mkktop/OCFM_V2/App/app_flow_calc.c

/**
 * @file    app_flow_calc.c
 * @brief   流量计算模块实现
 * @details  实现明渠流量计的核心计算功能
 *          - 瞬时流量计算(巴歇尔槽、三角堰、矩形堰)
 *          - 累计流量计算
 *          - 单位换算
 *
 * @note    水位数据来源: app_sensor 模块
 *          配置数据来源: app_config 模块
 */

#include "app_flow_calc.h"
#include "app_config.h"
#include "rtc.h"
#include "at24c02.h"
#include "FreeRTOS.h"
#include "task.h"
#include <string.h>

/*============================================================================*/
/*                           私有类型                                          */
/*============================================================================*/

/**
 * @brief 巴歇尔水槽参数结构体
 * @details 基于CJ/T 3008.3-1993《巴歇尔量水槽》标准
 *          计算公式: Q = K * H^n
 *          其中: Q-流量(L/s), H-水位(m), K-流量系数, n-指数
 * @note   巴歇尔槽不使用Kh水头修正
 */
typedef struct {
    uint32_t number_ID;        /**< 水槽规格编号 (1-25: 1-17标准型, 18-25大型) */
    float width;               /**< 喉道宽度 (m) */
    float factor;              /**< 流量系数 K */
    float n;                   /**< 指数 n */
    float water_level_down;    /**< 最小水位限制 (m) */
    float water_level_up;      /**< 最大水位限制 (m) */
    float flow_range_down;     /**< 最小流量限制 (L/s) */
    float flow_range_up;       /**< 最大流量限制 (L/s) */
} Water_Channel;

/**
 * @brief 三角堰参数结构体
 * @details 基于ISO 1438标准 (Kindsvater-Shen方法)
 *          计算公式: Q = K * (H + Kh)^n
 *          其中: Q-流量(L/s), H-水位(m), K-流量系数, n=2.5, Kh-水头修正
 *          常用角度: 90°, 60°, 45°, 30°, 22.5°
 */
typedef struct {
    uint32_t number_ID;        /**< 堰型编号 (1-5) */
    float angle_deg;           /**< 堰口角度 (度) */
    float factor;              /**< 流量系数 K (含Ce) */
    float n;                   /**< 指数 n (固定2.5) */
    float kh;                  /**< 水头修正 Kh (m) */
    float water_level_down;    /**< 最小水位限制 (m) */
    float water_level_up;      /**< 最大水位限制 (m) */
    float flow_range_down;     /**< 最小流量限制 (L/s) */
    float flow_range_up;       /**< 最大流量限制 (L/s) */
} TriangularWeir_t;

/**
 * @brief 矩形堰参数结构体
 * @details 基于ISO 1438标准 (Francis公式 + Kh修正)
 *          计算公式: Q = K * b * (H + Kh)^1.5
 *          其中: Q-流量(L/s), H-水位(m), K-流量系数, b-堰宽(m), Kh-水头修正
 *          常用堰宽: 0.5m, 1.0m, 1.5m, 2.0m
 */
typedef struct {
    uint32_t number_ID;        /**< 堰型编号 (1-4) */
    float width;               /**< 堰宽 (m) */
    float factor;              /**< 流量系数 K (约1.838) */
    float n;                   /**< 指数 n (固定1.5) */
    float kh;                  /**< 水头修正 Kh (m) */
    float water_level_down;    /**< 最小水位限制 (m) */
    float water_level_up;      /**< 最大水位限制 (m) */
    float flow_range_down;     /**< 最小流量限制 (L/s) */
    float flow_range_up;       /**< 最大流量限制 (L/s) */
} RectangularWeir_t;

/**
 * @brief 累计流量EEPROM存储结构体
 */
typedef struct {
    uint32_t magic;            /**< 校验标志 */
    double total_flow;         /**< 累计流量 (m³) */
    uint32_t total_time;       /**< 累计时长 (秒) */
    uint32_t reserved;         /**< 保留字段 */
} TotalFlowStorage_t;

/*============================================================================*/
/*                           私有变量                                          */
/*============================================================================*/

static float s_instant_flow = 0.0f;     /**< 当前瞬时流量 (根据配置的单位) */
static float s_instant_flow_lps = 0.0f;  /**< 当前瞬时流量 (原始L/s，未经单位转换) */
static volatile float s_last_water_level_m = 0.0f; /**< 上次流量计算使用的水位 (米) */
static double s_total_flow_m3 = 0.0;    /**< 累计流量 (m³) */
static uint32_t s_total_time_sec = 0;   /**< 累计时长 (秒) */
static uint8_t s_bkp_save_counter = 0;  /**< 备份寄存器保存计数器 (10秒周期) */
static uint16_t s_eeprom_save_counter = 0; /**< EEPROM保存计数器 (5分钟周期) */
static volatile uint8_t s_eeprom_save_pending = 0; /**< EEPROM待保存标志 */

/*============================================================================*/
/*                           私有数据                                          */
/*============================================================================*/

/**
 * @brief 巴歇尔水槽参数表 (CJ/T 3008.3-1993)
 * @note  索引0-24对应规格1-25 (1-5小型, 6-17标准型, 18-25大型)
 *        公式: Q = K * H^n (L/s, m)
 *        1-17号标准型: K/n 取自 CJ/T 3008.3-1993 表3
 *        18-25号大型型: K 取自 CJ/T 3008.3-1993 表4 / ISO 9826 (n=1.6)
 */
static const Water_Channel s_channel_tbl[25] = {
    {  1, 0.025,   60.4, 1.550, 0.015, 0.21,   0.09,     5.4 },   /* 0.025m  */
    {  2, 0.051,  120.7, 1.550, 0.015, 0.24,   0.18,    13.2 },   /* 0.051m  */
    {  3, 0.076,  177.1, 1.550, 0.030, 0.33,   0.77,    32.1 },   /* 0.076m  */
    {  4, 0.152,  381.2, 1.540, 0.030, 0.45,   1.50,   111.0 },   /* 0.152m  */
    {  5, 0.228,  535.4, 1.530, 0.030, 0.60,   2.50,   251.0 },   /* 0.228m  */
    {  6, 0.250,  561.0, 1.513, 0.030, 0.60,   3.00,   250.0 },   /* 0.250m  */
    {  7, 0.300,  679.0, 1.521, 0.030, 0.75,   3.50,   400.0 },   /* 0.300m  */
    {  8, 0.450, 1038.0, 1.537, 0.030, 0.75,   4.50,   630.0 },   /* 0.450m  */
    {  9, 0.600, 1403.0, 1.548, 0.050, 0.75,  12.50,   850.0 },   /* 0.60m   */
    { 10, 0.750, 1772.0, 1.557, 0.060, 0.75,  25.00,  1100.0 },   /* 0.75m   */
    { 11, 0.900, 2147.0, 1.565, 0.060, 0.75,  30.00,  1250.0 },   /* 0.90m   */
    { 12, 1.000, 2397.0, 1.569, 0.060, 0.80,  30.00,  1500.0 },   /* 1.00m   */
    { 13, 1.200, 2904.0, 1.577, 0.060, 0.80,  35.00,  2000.0 },   /* 1.20m   */
    { 14, 1.500, 3668.0, 1.586, 0.060, 0.80,  45.00,  2500.0 },   /* 1.50m   */
    { 15, 1.800, 4440.0, 1.593, 0.080, 0.80,  80.00,  3000.0 },   /* 1.80m   */
    { 16, 2.100, 5222.0, 1.599, 0.080, 0.80,  95.00,  3600.0 },   /* 2.10m   */
    { 17, 2.400, 6004.0, 1.605, 0.080, 0.80,   100.00,  4000.0 },   /* 2.40m   标准型最大喉宽(K外推) */
    { 18, 3.050,  7463.0, 1.600, 0.090, 1.07,  160.00,  8280.0 },   /* 3.05m   大型(10ft) */
    { 19, 3.660,  8859.0, 1.600, 0.090, 1.37,  190.00, 14680.0 },   /* 3.66m   大型(12ft) */
    { 20, 4.570, 10960.0, 1.600, 0.090, 1.67,  230.00, 25040.0 },   /* 4.57m   大型(15ft) */
    { 21, 6.100, 14450.0, 1.600, 0.090, 1.83,  310.00, 37970.0 },   /* 6.10m   大型(20ft) */
    { 22, 7.620, 17940.0, 1.600, 0.090, 1.83,  380.00, 47160.0 },   /* 7.62m   大型(25ft,K公式推导) */
    { 23, 9.140, 21440.0, 1.600, 0.090, 1.83,  460.00, 56330.0 },   /* 9.14m   大型(30ft) */
    { 24, 12.19, 28430.0, 1.600, 0.090, 1.83,  600.00, 74700.0 },   /* 12.19m  大型(40ft,K公式推导) */
    { 25, 15.24, 35410.0, 1.600, 0.090, 1.83,  750.00, 93040.0 },   /* 15.24m  大型(50ft) */
};

/**
 * @brief 三角堰参数表 (ISO 1438, Kindsvater-Shen方法)
 * @note  索引0-4对应规格1-5
 *        规格: 90°三角堰, 60°三角堰, 45°三角堰, 30°三角堰, 22.5°三角堰
 *        公式: Q = K * (H + Kh)^2.5 (L/s, m)
 *        K = Ce × (8/15) × √(2g) × tan(θ/2) × 1000
 *        Ce, Kh 由 Kindsvater-Shen 曲线拟合得到
 *        Ce = 0.607165052 - 0.000874467θ + 6.103933e-6 θ²
 *        Kh(ft) = 0.01449 - 0.0003396θ + 3.298e-6 θ² - 1.062e-8 θ³
 *        Kh(m) = Kh(ft) × 0.3048; 90°时 Kh=0.00085m (ISO 1438-1 标准 0.85mm)
 */
static const TriangularWeir_t s_triangular_weir_tbl[5] = {
    { 1,  90.0f, 1365.0f, 2.50f, 0.00085f, 0.05f, 0.40f,  0.88f,  140.7f },  /* 90° Ce=0.5779 Kh=0.00085m (ISO1438 0.85mm) */
    { 2,  60.0f,  786.4f, 2.50f, 0.00113f, 0.05f, 0.35f,  0.48f,   57.7f },  /* 60° Ce=0.5767 Kh=0.00113m */
    { 3,  45.0f,  567.8f, 2.50f, 0.00150f, 0.05f, 0.30f,  0.35f,   28.4f },  /* 45° Ce=0.5802 Kh=0.00150m */
    { 4,  30.0f,  371.1f, 2.50f, 0.00213f, 0.05f, 0.25f,  0.23f,   11.9f },  /* 30° Ce=0.5864 Kh=0.00213m */
    { 5,  22.5f,  277.5f, 2.50f, 0.00256f, 0.05f, 0.25f,  0.18f,    8.90f }, /* 22.5° Ce=0.5906 Kh=0.00256m */
};

/**
 * @brief 矩形堰参数表 (ISO 1438, Francis公式)
 * @note  索引0-3对应规格1-4
 *        规格: 0.5m堰宽, 1.0m堰宽, 1.5m堰宽, 2.0m堰宽
 *        公式: Q = K * b * (H + Kh)^1.5 (L/s, m) - 无侧收缩（全宽堰）
 *        K = Cd × (2/3) × √(2g) × 1000, Cd=0.622 (Francis)
 *        Kh ≈ 0.001m (Kindsvater-Carter 水头修正)
 */
static const RectangularWeir_t s_rectangular_weir_tbl[4] = {
    { 1, 0.50f, 1838.0f, 1.50f, 0.001f, 0.05f, 0.50f,  10.6f,  326.0f },   /* 0.5m堰宽 */
    { 2, 1.00f, 1838.0f, 1.50f, 0.001f, 0.05f, 0.60f,  21.2f,  856.0f },   /* 1.0m堰宽 */
    { 3, 1.50f, 1838.0f, 1.50f, 0.001f, 0.05f, 0.70f,  31.8f, 1618.0f },   /* 1.5m堰宽 */
    { 4, 2.00f, 1838.0f, 1.50f, 0.001f, 0.05f, 0.80f,  42.3f, 2635.0f },   /* 2.0m堰宽 */
};

/**
 * @brief  计算巴歇尔槽瞬时流量
 * @param  water_level_m: 水位 (米)
 * @param  channel: 水槽参数指针
 * @param  wl_down: 用户配置的水位下限 (m)
 * @param  wl_up: 用户配置的水位上限 (m)
 * @retval 瞬时流量 (L/s)，水位无效时返回0
 * @note   公式: Q = K * H^n，超量程时限制在最大值
 */
static float parshall_flow_Ls(float water_level_m, const Water_Channel *channel,
                              float wl_down, float wl_up)
{
    float Q = 0.0f;

    /* 检查空指针 */
    if (channel == NULL) {
        return 0.0f;
    }

    /* 水位高于上限: 钳位到上限计算 */
    if (water_level_m > wl_up) {
        Q = channel->factor * powf(wl_up, channel->n);
    }
    /* 水位低于下限 (扣除 0.1mm 容差，防止浮点精度边界误判)
     * 例: 高度800mm - 距离720mm 经 float 运算后为 0.07999998m，
     * 略小于下限 0.08f，数学上应相等却被判为"低于下限"，故加容差 */
    else if (water_level_m < wl_down - 0.0001f) {
        Q = 0.0f;
    }
    /* 水位在有效范围内 (含浮点容差区间 [wl_down-tol, wl_up]) */
    else {
        Q = channel->factor * powf(water_level_m, channel->n);
    }

    return Q;
}

/**
 * @brief  瞬时流量单位转换
 * @param  flow_l_s: 瞬时流量 (L/s)
 * @param  unit: 目标单位
 * @retval 转换后的瞬时流量值
 */
static float flow_convert_instant(float flow_l_s, flow_unit_t unit)
{
    switch (unit) {
        case FLOW_UNIT_L_S:
            return flow_l_s;
        case FLOW_UNIT_L_MIN:
            return flow_l_s * 60.0f;
        case FLOW_UNIT_L_H:
            return flow_l_s * 3600.0f;
        case FLOW_UNIT_M3_H:
            return flow_l_s * 3.6f;
        case FLOW_UNIT_M3_S:
            return flow_l_s / 1000.0f;
        case FLOW_UNIT_M3_MIN:
            return flow_l_s / 1000.0f * 60.0f;
        case FLOW_UNIT_T_H:
            return flow_l_s * 3.6f;
        case FLOW_UNIT_G_H:
            return flow_l_s * 3600.0f / 3.785411784f;
        default:
            return flow_l_s;
    }
}

/**
 * @brief  计算三角堰瞬时流量 (Kindsvater-Shen方法)
 * @param  water_level_m: 水位 (米)
 * @param  weir: 三角堰参数指针
 * @param  wl_down: 用户配置的水位下限 (m)
 * @param  wl_up: 用户配置的水位上限 (m)
 * @retval 瞬时流量 (L/s)，水位无效时返回0
 * @note   公式: Q = K * (H + Kh)^n，超量程时限制在最大值
 */
static float triangular_weir_flow_Ls(float water_level_m, const TriangularWeir_t *weir,
                                     float wl_down, float wl_up)
{
    float Q = 0.0f;
    float he;

    if (weir == NULL) {
        return 0.0f;
    }

    /* 水位高于上限: 钳位到上限计算 */
    if (water_level_m > wl_up) {
        he = wl_up + weir->kh;
        Q = weir->factor * powf(he, weir->n);
    }
    /* 水位低于下限 (扣除 0.1mm 容差，防止浮点精度边界误判) */
    else if (water_level_m < wl_down - 0.0001f) {
        Q = 0.0f;
    }
    /* 水位在有效范围内 (含浮点容差区间) */
    else {
        he = water_level_m + weir->kh;
        Q = weir->factor * powf(he, weir->n);
    }

    return Q;
}

/**
 * @brief  矩形堰 Kindsvater-Carter 收缩流量系数 Ce (ISO 1438-1 Figure 5)
 * @param  bB: 堰宽/渠宽比 b/B (0.2~1.0)
 * @param  hP: 水头/堰高比 h/P
 * @retval 流量系数 Ce (无量纲)
 * @note   按 b/B 分段(0.2~1.0 共9档) + h/P 线性插值查表
 *         表值取自 ISO 1438-1:2008 Figure 5 (Kindsvater-Carter 方法)
 *         不确定度: h/P<1.0 时 <=1.5%
 */
static float rect_weir_Ce(float bB, float hP)
{
    /* b/B = 1.0, 0.9, 0.8, ..., 0.2 共9档, 每档 h/P = 0.1,0.2,...,1.0 共8点 */
    static const float ce_tbl[9][8] = {
        /* h/P:  0.1    0.2    0.3    0.4    0.5    0.6    0.8    1.0  */
        /*1.0*/{0.610f,0.619f,0.627f,0.636f,0.644f,0.652f,0.669f,0.685f},
        /*0.9*/{0.609f,0.617f,0.626f,0.634f,0.642f,0.651f,0.668f,0.684f},
        /*0.8*/{0.608f,0.616f,0.624f,0.633f,0.641f,0.649f,0.666f,0.682f},
        /*0.7*/{0.606f,0.614f,0.623f,0.631f,0.639f,0.648f,0.664f,0.680f},
        /*0.6*/{0.603f,0.612f,0.620f,0.629f,0.637f,0.646f,0.662f,0.678f},
        /*0.5*/{0.600f,0.609f,0.617f,0.626f,0.634f,0.643f,0.659f,0.675f},
        /*0.4*/{0.596f,0.605f,0.613f,0.622f,0.630f,0.639f,0.655f,0.671f},
        /*0.3*/{0.590f,0.599f,0.608f,0.616f,0.625f,0.633f,0.650f,0.666f},
        /*0.2*/{0.583f,0.592f,0.601f,0.609f,0.618f,0.626f,0.643f,0.659f},
    };
    static const float hP_axis[8] = {0.1f,0.2f,0.3f,0.4f,0.5f,0.6f,0.8f,1.0f};
    int i_bB, i_hP;
    float w;

    if (bB > 1.0f) bB = 1.0f;            /* b/B 上限 1.0 (全宽堰) */
    if (bB < 0.2f) bB = 0.2f;            /* b/B 下限 0.2 (强收缩) */
    if (hP < 0.0f) hP = 0.0f;
    if (hP > 1.0f) hP = 1.0f;            /* KC 表适用 h/P<=1.0, 超出按1.0 */

    /* b/B 插值索引: 1.0->0, 0.9->1, ..., 0.2->8 (步长0.1) */
    {
        float fidx = (1.0f - bB) * 10.0f;
        i_bB = (int)fidx;
        if (i_bB > 7) i_bB = 7;          /* 保证 i_bB+1 不越界 */
        w = fidx - i_bB;
    }
    /* h/P 插值索引: 0.1->0, 0.2->1, ..., 0.8->6, 1.0->7 (非均匀: 0.6->0.8 跨0.2) */
    /* 简化: h/P<=0.6 用步长0.1, 0.6~0.8 跨0.2, 0.8~1.0 跨0.2 */
    {
        i_hP = 0;
        while (i_hP < 7 && hP > hP_axis[i_hP + 1]) i_hP++;
    }

    /* 双线性插值 (b/B, h/P) */
    {
        float Ce00 = ce_tbl[i_bB][i_hP];
        float Ce10 = ce_tbl[i_bB + 1][i_hP];
        float Ce01 = ce_tbl[i_bB][i_hP + 1];
        float Ce11 = ce_tbl[i_bB + 1][i_hP + 1];
        float hP_lo = hP_axis[i_hP];
        float hP_hi = hP_axis[i_hP + 1];
        float wh = (hP - hP_lo) / (hP_hi - hP_lo);
        if (wh < 0.0f) wh = 0.0f;
        if (wh > 1.0f) wh = 1.0f;
        float Ce_b_lo = Ce00 + w * (Ce10 - Ce00);
        float Ce_b_hi = Ce01 + w * (Ce11 - Ce01);
        return Ce_b_lo + wh * (Ce_b_hi - Ce_b_lo);
    }
}

/**
 * @brief  矩形堰 Kindsvater-Carter 宽度修正 Kb (ISO 1438-1 Figure 6)
 * @param  bB: 堰宽/渠宽比 b/B (0.2~1.0)
 * @retval 宽度修正 Kb (m), 全宽堰(b/B=1)返回0
 */
static float rect_weir_Kb(float bB)
{
    static const float kb_tbl[9] = {
        /* b/B: 1.0  0.9   0.8   0.7   0.6   0.5   0.4   0.3   0.2  */
              0.0f,0.0018f,0.0022f,0.0024f,0.0026f,0.0028f,0.0030f,0.0032f,0.0034f
    };
    int idx;
    if (bB > 1.0f) bB = 1.0f;
    if (bB < 0.2f) bB = 0.2f;
    idx = (int)((1.0f - bB) * 10.0f + 0.5f);   /* 四舍五入到最近档 */
    if (idx > 8) idx = 8;
    return kb_tbl[idx];
}

/**
 * @brief  计算矩形堰瞬时流量 (Kindsvater-Carter 方法, ISO 1438-1)
 * @param  water_level_m: 水位 (米)
 * @param  weir: 矩形堰参数指针
 * @param  wl_down: 用户配置的水位下限 (m)
 * @param  wl_up: 用户配置的水位上限 (m)
 * @retval 瞬时流量 (L/s)，水位无效时返回0
 * @note   公式: Q = Ce * (2/3) * sqrt(2g) * be * he^1.5
 *         he = H + Kh (Kh=0.001m 有效水头)
 *         全宽堰(B=0或B<=b): be=b, Ce=0.602+0.083*(H/P)
 *         收缩堰(B>b):       be=b+Kb, Ce 按 b/B,h/P 查 ISO Figure 5
 *         需堰高 P(weir_height) 配置; P=0 或 h/P>1.0 时回退到 Francis 固定系数
 *         (ISO KC 法适用范围: h/P<=1.0, P>=0.1m, h>=0.03m)
 *         超量程时钳位到上限计算
 */
static float rectangular_weir_flow_Ls(float water_level_m, const RectangularWeir_t *weir,
                                      float wl_down, float wl_up)
{
    float Q = 0.0f;
    float he, effective_width;
    float use_kc;   /* 1=Kindsvater-Carter, 0=Francis回退 */

    if (weir == NULL) {
        return 0.0f;
    }

    float B = app_config_get_channel_width() / 1000.0f;
    float b = weir->width;
    float P = app_config_get_weir_height() / 1000.0f;   /* 堰高(m), 0=未配置 */
    int   contracted = (B > 0.0f && b < B);             /* 是否收缩堰 */

    /* 选定计算用水位 h: 超上限钳位, 低于下限返回0 */
    if (water_level_m > wl_up) {
        water_level_m = wl_up;
    } else if (water_level_m < wl_down - 0.0001f) {
        return 0.0f;
    }
    /* 浮点容差区间内正常计算 */

    /* KC 法启用条件: 配置了堰高 P 且 h/P<=1.0 (ISO 适用范围)
     * P=0(未配置) 或 h/P>1.0(超范围) 时回退 Francis 固定系数,
     * 避免 KC 外推失真 */
    use_kc = (P > 0.0f && (water_level_m / P) <= 1.0f) ? 1.0f : 0.0f;

    he = water_level_m + weir->kh;

    /* ---- 有效宽度 be ---- */
    if (use_kc) {
        if (contracted) {
            float bB = b / B;
            effective_width = b + rect_weir_Kb(bB);
        } else {
            effective_width = b;      /* 全宽堰 be=b, Kb=0 */
        }
    } else {
        /* Francis 回退: 收缩堰 b-0.2H */
        if (contracted) {
            effective_width = b - 0.2f * water_level_m;
            if (effective_width < 0.0f) effective_width = 0.0f;
        } else {
            effective_width = b;
        }
    }

    /* ---- 流量 ---- */
    if (use_kc) {
        /* Q = Ce * (2/3)*sqrt(2g)*1000 * be * he^1.5, base≈2952.46 */
        const float kc_base = 2952.46f;
        float Ce;
        float hP = water_level_m / P;
        if (contracted) {
            float bB = b / B;
            Ce = rect_weir_Ce(bB, hP);   /* 此处 hP<=1.0 由启用条件保证 */
        } else {
            /* 全宽堰 Ce = 0.602 + 0.083*(h/P) (ISO 1438-1) */
            Ce = 0.602f + 0.083f * hP;
        }
        Q = Ce * kc_base * effective_width * powf(he, 1.5f);
    } else {
        /* Francis 回退: K=1838 */
        Q = weir->factor * effective_width * powf(he, weir->n);
    }

    return Q;
}

/**
 * @brief  计算瞬时流量 (统一入口)
 * @param  water_level_m: 水位 (米)
 * @retval 瞬时流量 (L/s) - 固定返回基准单位
 */
static float flow_calc_instant(float water_level_m)
{
    float Q_l_s = 0.0f;
    uint32_t cid = app_config_get_channel_id();
    uint32_t canals_type = app_config_get_canals_type();
    float wl_up = app_config_get_water_level_up();
    float wl_down = app_config_get_water_level_down();

    /* 边界保护: channel_id 必须从1开始, 否则返回0 */
    if (cid < 1) return 0.0f;

    /* 按渠类型校验 channel_id 范围 */
    if (canals_type == PARSHALL_FLUME && cid > 25) return 0.0f;
    if (canals_type == TRIANGULAR_WEIR && cid > 5) return 0.0f;
    if (canals_type == RECTANGULAR_WEIR && cid > 4) return 0.0f;

    switch (canals_type) {
        case PARSHALL_FLUME:
            Q_l_s = parshall_flow_Ls(water_level_m, &s_channel_tbl[cid - 1],
                                     wl_down, wl_up);
            break;
        case TRIANGULAR_WEIR:
            Q_l_s = triangular_weir_flow_Ls(water_level_m, &s_triangular_weir_tbl[cid - 1],
                                            wl_down, wl_up);
            break;
        case RECTANGULAR_WEIR:
            Q_l_s = rectangular_weir_flow_Ls(water_level_m, &s_rectangular_weir_tbl[cid - 1],
                                             wl_down, wl_up);
            break;
        default:
            Q_l_s = 0.0f;
            break;
    }
    return Q_l_s;
}

/*============================================================================*/
/*                           对外接口                                           */
/*============================================================================*/

/**
 * @brief  保存累计流量和累计时长到备份寄存器
 * @note   DR1/DR2: 累计流量(double), DR3: magic
 *         DR4: 累计时长(uint32)
 */
void flow_calc_save_total(void)
{
    uint32_t buf[2];
    double snapshot;
    uint32_t time_snapshot;
    extern RTC_HandleTypeDef hrtc;

    /* 原子快照：double在Cortex-M4上不是原子读写 */
    taskENTER_CRITICAL();
    snapshot = s_total_flow_m3;
    time_snapshot = s_total_time_sec;
    taskEXIT_CRITICAL();

    /* 保存累计流量 */
    memcpy(buf, &snapshot, sizeof(double));
    HAL_RTCEx_BKUPWrite(&hrtc, RTC_BKP_DR1, buf[0]);
    HAL_RTCEx_BKUPWrite(&hrtc, RTC_BKP_DR2, buf[1]);
    HAL_RTCEx_BKUPWrite(&hrtc, RTC_BKP_DR3, TOTAL_FLOW_MAGIC_NUMBER);

    /* 保存累计时长 */
    HAL_RTCEx_BKUPWrite(&hrtc, RTC_BKP_DR4, time_snapshot);
}

/**
 * @brief  从备份寄存器加载累计流量和累计时长
 * @retval 1: 加载成功, 0: 数据无效
 */
static uint8_t flow_calc_load_from_backup(void)
{
    uint32_t buf[2];
    uint32_t magic;
    double total_flow = 0.0;
    uint32_t total_time = 0;
    extern RTC_HandleTypeDef hrtc;

    /* 校验magic number */
    magic = HAL_RTCEx_BKUPRead(&hrtc, RTC_BKP_DR3);
    if (magic != TOTAL_FLOW_MAGIC_NUMBER) {
        return 0;
    }

    buf[0] = HAL_RTCEx_BKUPRead(&hrtc, RTC_BKP_DR1);
    buf[1] = HAL_RTCEx_BKUPRead(&hrtc, RTC_BKP_DR2);
    memcpy(&total_flow, buf, sizeof(double));

    /* 检查是否为有效数据 */
    if (total_flow < 0.0) {
        return 0;
    }
    if (total_flow >= 1e12) {
        total_flow = 999999999999.0;
    }

    /* 读取累计时长 */
    total_time = HAL_RTCEx_BKUPRead(&hrtc, RTC_BKP_DR4);

    s_total_flow_m3 = total_flow;
    s_total_time_sec = total_time;
    return 1;
}

/**
 * @brief  保存累计流量和累计时长到EEPROM
 * @retval 1: 成功, 0: 失败
 */
static uint8_t flow_calc_save_to_eeprom(void)
{
    TotalFlowStorage_t storage;

    storage.magic = TOTAL_FLOW_MAGIC_NUMBER;
    taskENTER_CRITICAL();
    storage.total_flow = s_total_flow_m3;
    storage.total_time = s_total_time_sec;
    taskEXIT_CRITICAL();
    storage.reserved = 0;

    return at24c02_write_buffer(TOTAL_FLOW_EEPROM_ADDR, sizeof(TotalFlowStorage_t),
                                (uint8_t*)&storage);
}

/**
 * @brief  从EEPROM加载累计流量和累计时长
 * @retval 1: 加载成功, 0: 数据无效
 */
static uint8_t flow_calc_load_from_eeprom(void)
{
    TotalFlowStorage_t storage;

    if (at24c02_read_buffer(TOTAL_FLOW_EEPROM_ADDR, sizeof(TotalFlowStorage_t),
                            (uint8_t*)&storage) != 1) {
        return 0;
    }

    /* 校验magic number */
    if (storage.magic != TOTAL_FLOW_MAGIC_NUMBER) {
        return 0;
    }

    /* 检查是否为有效数据 */
    if (storage.total_flow < 0.0) {
        return 0;
    }
    if (storage.total_flow >= 1e12) {
        storage.total_flow = 999999999999.0;
    }

    /* 检查累计时长是否有效 */
    if (storage.total_time > 0xFFFFFFFFUL / 2) {
        storage.total_time = 0;
    }

    s_total_flow_m3 = storage.total_flow;
    s_total_time_sec = storage.total_time;
    return 1;
}

/**
 * @brief  从备份寄存器/EEPROM加载累计流量和累计时长
 * @note   优先从备份寄存器读取，失败则从EEPROM读取
 */
void flow_calc_load_total(void)
{
    /* 优先从备份寄存器加载 */
    if (flow_calc_load_from_backup()) {
        return;
    }

    /* 备份寄存器无效，尝试从EEPROM加载 */
    if (flow_calc_load_from_eeprom()) {
        /* 同步到备份寄存器 */
        flow_calc_save_total();
        return;
    }

    /* 两者都无效，使用默认值0 */
    s_total_flow_m3 = 0.0;
    s_total_time_sec = 0;
}

/**
 * @brief  更新流量计算 (每秒调用)
 * @param  water_level_m: 水位 (米), 传入负值或0时不做流量计算
 * @note   计算瞬时流量并累加累计流量和累计时长
 *         - 瞬时流量: 根据配置的单位显示
 *         - 累计流量: 固定使用 m³
 *         - 累计时长: 单位 秒
 *         - 每10秒保存到备份寄存器
 *         - 每5分钟保存到EEPROM
 */
void flow_calc_update(float water_level_m)
{
    /* 保存计算用的水位快照 */
    s_last_water_level_m = water_level_m;

    /* 传感器离线时累计时长不递增 */
    if (water_level_m <= 0.0f) {
        s_instant_flow_lps = 0.0f;
        s_instant_flow = 0.0f;
        return;
    }

    /* 计算瞬时流量 (L/s) */
    s_instant_flow_lps = flow_calc_instant(water_level_m);
    s_instant_flow = s_instant_flow_lps;

    /* 累加累计流量: L/s * 1s = L, 除以1000转m³
     * 注意：使用double精度计算，避免float除法丢失精度
     * 累计时长与累计流量作为一组保护，防止与reset_total/set_total竞态 */
    taskENTER_CRITICAL();
    s_total_time_sec++;
    s_total_flow_m3 += (double)s_instant_flow_lps / 1000.0;
    taskEXIT_CRITICAL();

    /* 单位转换 */
    if (app_config_get_instant_unit() != FLOW_UNIT_L_S) {
        s_instant_flow = flow_convert_instant(s_instant_flow, app_config_get_instant_unit());
    }

    /* 每2秒保存累计流量到备份寄存器 */
    if (++s_bkp_save_counter >= 2) {
        s_bkp_save_counter = 0;
        flow_calc_save_total();
    }

    /* 每5分钟设置EEPROM保存标志 (5分钟 = 300秒) */
    if (++s_eeprom_save_counter >= 300) {
        s_eeprom_save_counter = 0;
        s_eeprom_save_pending = 1;
    }
}

/**
 * @brief  处理EEPROM保存请求 (在主循环中调用)
 * @note   避免在定时器中直接操作I2C，防止阻塞
 */
void flow_calc_process(void)
{
    if (s_eeprom_save_pending) {
        s_eeprom_save_pending = 0;
        if (app_config_eeprom_lock()) {
            flow_calc_save_to_eeprom();
            app_config_eeprom_unlock();
        } else {
            s_eeprom_save_pending = 1;  /* 获取锁失败, 下次重试 */
        }
    }
}

/**
 * @brief  获取当前瞬时流量
 * @retval 瞬时流量 (根据配置的单位)
 */
float flow_calc_get_instant(void)
{
    return s_instant_flow;
}

/**
 * @brief  获取当前瞬时流量 (原始L/s)
 * @retval 瞬时流量 (L/s，未经单位转换)
 */
float flow_calc_get_instant_lps(void)
{
    return s_instant_flow_lps;
}

/**
 * @brief  获取上次流量计算使用的水位
 * @retval 水位 (米)
 */
float flow_calc_get_last_water_level(void)
{
    return s_last_water_level_m;
}

/**
 * @brief  获取累计流量
 * @retval 累计流量 (m³)
 */
double flow_calc_get_total(void)
{
    double val;
    taskENTER_CRITICAL();
    val = s_total_flow_m3;
    taskEXIT_CRITICAL();
    return val;
}

/**
 * @brief  清零累计流量和累计时长
 */
void flow_calc_reset_total(void)
{
    taskENTER_CRITICAL();
    s_total_flow_m3 = 0.0;
    s_total_time_sec = 0;
    taskEXIT_CRITICAL();
    flow_calc_save_total();         /* 同步清除备份寄存器 (快速, 无阻塞) */
    s_eeprom_save_pending = 1;      /* 延迟写入EEPROM (由flow_calc_process在主循环执行) */
}

void flow_calc_set_total(double value)
{
    if (value < 0.0 || value >= 1e12) return;
    taskENTER_CRITICAL();
    s_total_flow_m3 = value;
    taskEXIT_CRITICAL();
    flow_calc_save_total();
    s_eeprom_save_pending = 1;
}

/**
 * @brief  获取累计时长
 * @retval 累计时长 (秒)
 */
uint32_t flow_calc_get_total_time(void)
{
    return s_total_time_sec;
}

/**
 * @brief  获取当前槽型的理论最大流量 (m³/h)
 * @note   用配置的 water_level_up 代入流量公式计算
 */
static float get_channel_max_m3h(void)
{
    uint32_t cid = app_config_get_channel_id();
    uint32_t canals_type = app_config_get_canals_type();
    float max_lps = 0.0f;
    float wl_up = app_config_get_water_level_up();

    if (cid < 1) return 0.0f;

    switch (canals_type) {
        case PARSHALL_FLUME:
            if (cid > 25) return 0.0f;
            max_lps = parshall_flow_Ls(wl_up, &s_channel_tbl[cid - 1],
                                       0.0f, wl_up);
            break;
        case TRIANGULAR_WEIR:
            if (cid > 5) return 0.0f;
            max_lps = triangular_weir_flow_Ls(wl_up, &s_triangular_weir_tbl[cid - 1],
                                              0.0f, wl_up);
            break;
        case RECTANGULAR_WEIR:
            if (cid > 4) return 0.0f;
            max_lps = rectangular_weir_flow_Ls(wl_up, &s_rectangular_weir_tbl[cid - 1],
                                               0.0f, wl_up);
            break;
        default:
            return 0.0f;
    }

    return max_lps * 3.6f;
}

/**
 * @brief  获取当前槽型的最大流量上限 (m³/h)
 * @note   理论最大值 × 120% 裕量，用于限制4-20mA量程设定
 */
float flow_calc_get_max_flow_m3h(void)
{
    return get_channel_max_m3h() * 1.2f;
}

/**
 * @brief  获取当前槽型的理论最大流量 (m³/h)
 * @note   不含余量，用于自动设置量程
 */
float flow_calc_get_channel_max_m3h(void)
{
    return get_channel_max_m3h();
}

/**
 * @brief  根据当前槽型/规格获取参数表的默认水位上下限
 * @param  up:   输出水位上限 (m)
 * @param  down: 输出水位下限 (m)
 * @retval 1: 成功获取, 0: 参数无效
 * @note   仅从硬编码参数表读取默认值，不读取用户配置
 */
uint8_t flow_calc_get_default_water_level(float *up, float *down)
{
    uint32_t cid = app_config_get_channel_id();
    uint32_t canals_type = app_config_get_canals_type();

    if (cid < 1) return 0;

    switch (canals_type) {
        case PARSHALL_FLUME:
            if (cid > 25) return 0;
            *up = s_channel_tbl[cid - 1].water_level_up;
            *down = s_channel_tbl[cid - 1].water_level_down;
            break;
        case TRIANGULAR_WEIR:
            if (cid > 5) return 0;
            *up = s_triangular_weir_tbl[cid - 1].water_level_up;
            *down = s_triangular_weir_tbl[cid - 1].water_level_down;
            break;
        case RECTANGULAR_WEIR:
            if (cid > 4) return 0;
            *up = s_rectangular_weir_tbl[cid - 1].water_level_up;
            *down = s_rectangular_weir_tbl[cid - 1].water_level_down;
            break;
        default:
            return 0;
    }
    return 1;
}
