mkktop/OCFM_V2/App/app_model.c

/**
 * @file app_model.c
 * @brief 应用数据模型实现
 * @details 实现数据模型的初始化和更新逻辑
 */

#include "app_model.h"
#include "app_flow_calc.h"
#include "app_current.h"
#include "app_sensor.h"
#include "app_config.h"
#include "global.h"
#include "rtc_time.h"
#include <stdio.h>

/**
 * @brief 全局应用数据模型实例
 */
AppDataModel g_app_model = {0};

/**
 * @brief 初始化应用数据模型
 */
void app_model_init(void)
{
    g_app_model.total_time_sec = 0;
    g_app_model.total_flow = 0.0;
    g_app_model.instant_flow = 0.0f;
    g_app_model.water_level_m = 0.0f;
    g_app_model.sensor_online = 0;
}

/**
 * @brief 格式化累计时长为字符串
 */
static void format_total_time(uint32_t total_sec, char *buf, size_t buf_size)
{
    uint32_t days = total_sec / (24 * 3600);
    uint32_t hours = (total_sec % (24 * 3600)) / 3600;
    uint32_t minutes = (total_sec % 3600) / 60;
    uint32_t seconds = total_sec % 60;

    snprintf(buf, buf_size, "%lu day %02lu:%02lu:%02lu",
             (unsigned long)days,
             (unsigned long)hours,
             (unsigned long)minutes,
             (unsigned long)seconds);
}

static uint32_t count_integer_digits_from_string(const char *str)
{
    uint32_t digits = 0;

    if (*str == '-') {
        str++;
    }

    while (*str >= '0' && *str <= '9') {
        digits++;
        str++;
    }

    return digits > 0 ? digits : 1;
}

static uint32_t limit_instant_flow_decimals(uint32_t point_num, uint32_t integer_digits)
{
    uint32_t max_decimals = point_num;

    if (integer_digits > 8) {
        max_decimals = 0;
    } else if (integer_digits > 7 && max_decimals > 1) {
        max_decimals = 1;
    } else if (integer_digits > 6 && max_decimals > 2) {
        max_decimals = 2;
    }

    return max_decimals;
}

static void format_instant_flow(float value, uint32_t point_num, char *buf, size_t buf_size)
{
    char fmt[8];
    uint32_t decimals = point_num;
    uint32_t limited_decimals;

    do {
        snprintf(fmt, sizeof(fmt), "%%.%luf", (unsigned long)decimals);
        snprintf(buf, buf_size, fmt, value);

        limited_decimals = limit_instant_flow_decimals(
            point_num,
            count_integer_digits_from_string(buf));

        if (limited_decimals >= decimals) {
            break;
        }

        decimals = limited_decimals;
    } while (1);
}

/**
 * @brief 更新应用数据模型
 * @details 每秒调用一次，更新：
 *       - 当前时间
 *       - 累计时长
 *       - 流量数据
 *       - 传感器状态
 */
void app_model_update(void)
{
    /* 从 RTC 获取当前时间 */
    RTC_TimeData time_data;
    RTC_Time_Get(&time_data);

    snprintf(g_app_model.time_str, sizeof(g_app_model.time_str),
             "%04d/%02d/%02d %02d:%02d:%02d",
             time_data.year, time_data.month, time_data.date,
             time_data.hour, time_data.minute, time_data.second);

    snprintf(g_app_model.time_short_str, sizeof(g_app_model.time_short_str),
             "%02d:%02d",
             time_data.hour, time_data.minute);

    /* 同步累计时长 */
    g_app_model.total_time_sec = flow_calc_get_total_time();
    format_total_time(g_app_model.total_time_sec,
                      g_app_model.total_time_str,
                      sizeof(g_app_model.total_time_str));

    /* 流量计算在 freertos.c 的 flow_refresh_fun 定时器中更新 */

    /* 同步流量数据 */
    g_app_model.instant_flow = flow_calc_get_instant();
    g_app_model.total_flow = flow_calc_get_total();

    /* 格式化流量字符串 - 使用配置的小数位数 */
    uint32_t point_num = app_config_get_point_num();
    uint32_t sum_point = app_config_get_sum_point();
    char fmt[8];

    /* 瞬时流量 */
    format_instant_flow(g_app_model.instant_flow, point_num,
                        g_app_model.instant_flow_str,
                        sizeof(g_app_model.instant_flow_str));

    /* 累计流量 */
    snprintf(fmt, sizeof(fmt), "%%.%luf", (unsigned long)sum_point);
    snprintf(g_app_model.total_flow_str, sizeof(g_app_model.total_flow_str),
             fmt, g_app_model.total_flow);

    /* 计算4-20mA输出电流 (4mA/20mA量程单位固定m³/h) */
    app_current_format_ma(flow_calc_get_instant_lps() * 3.6f,
                          g_app_model.current_ma_str,
                          sizeof(g_app_model.current_ma_str));

    /* 同步传感器状态 (使用快照保证多字段一致性) */
    {
        SensorData_t sensor_snap;
        app_sensor_get_snapshot(&sensor_snap);

        g_app_model.water_level_m = sensor_snap.water_level_m;
        g_app_model.temperature_x10 = sensor_snap.temperature_x10;
        g_app_model.sensor_online = sensor_snap.is_online;

        /* 格式化水位字符串 */
        if (g_app_model.sensor_online) {
            snprintf(g_app_model.water_level_str, sizeof(g_app_model.water_level_str),
                     "L:%.3fm", g_app_model.water_level_m);
        } else {
            snprintf(g_app_model.water_level_str, sizeof(g_app_model.water_level_str),
                     "L:error");
        }

        /* 格式化温度字符串 */
        if (sensor_snap.temp_valid)
        {
            snprintf(g_app_model.temperature_str, sizeof(g_app_model.temperature_str),
                     "%.1f\xC2\xB0""C", g_app_model.temperature_x10 / 10.0f);
        }
        else
        {
            snprintf(g_app_model.temperature_str, sizeof(g_app_model.temperature_str),
                     "--\xC2\xB0""C");
        }
    }
}
